SteveCooling/MidiKeys/PlatformIO/MidiKeys/include/lut.h

/*
* Lookup tables
*/

static const int midi_freq[128] = {
  8,
  8,
  9,
  9,
  10,
  10,
  11,
  12,
  12,
  13,
  14,
  15,
  16,
  17,
  18,
  19,
  20,
  21,
  23,
  24,
  25,
  27,
  29,
  30,
  32,
  34,
  36,
  38,
  41,
  43,
  46,
  48,
  51,
  55,
  58,
  61,
  65,
  69,
  73,
  77,
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
};
